artemisamsx/artemisa/simulation/include/mem/62256_tb.v

`include "62256.v"

`include "utils/asserts.v"
`include "utils/clock.v"

`timescale 1ns/100ps

module ic62256_ram_tb;

    reg ncs = 1, nwe = 1, noe = 1;
    reg [14:0] addr;
    reg [7:0] data_out;

    wire [7:0] data = data_out === 8'bz ? 8'bz : data_out;

    ic62256_ram dut(ncs, nwe, noe, addr, data);
    clock clock(clk);

    initial
    begin
        $dumpfile("62256.vcd");
        $dumpvars;

        /***
         * Must write data at 0x1234
         */        
        #20 addr = 15'h1234;

        `CLOCK_NEXT_HALF(clk, 20);
        ncs = 0;
        data_out = 8'h42;

        `CLOCK_NEXT_HALF(clk, 20);
        nwe = 0;

        `CLOCK_NEXT_HALF(clk, 20);
        ncs = 1;
        nwe = 1;

        `CLOCK_NEXT(clk, 20);
        data_out = 8'bz;

        /***
         * Must read data from 0x1234
         */
        addr = 15'h1234;
        `CLOCK_NEXT_HALF(clk, 20);
        `ASSERT(data === 8'bz);
        ncs = 0;
        noe = 0;

        repeat(2) `CLOCK_NEXT_HALF(clk, 20);
        `ASSERT(data === 8'h42);
        ncs = 1;
        noe = 1;

        `CLOCK_NEXT(clk, 0);
        $finish;
    end
endmodule
